Goji2100/Spresense-LCD-Board/DOC/IMG_4674.jpeg

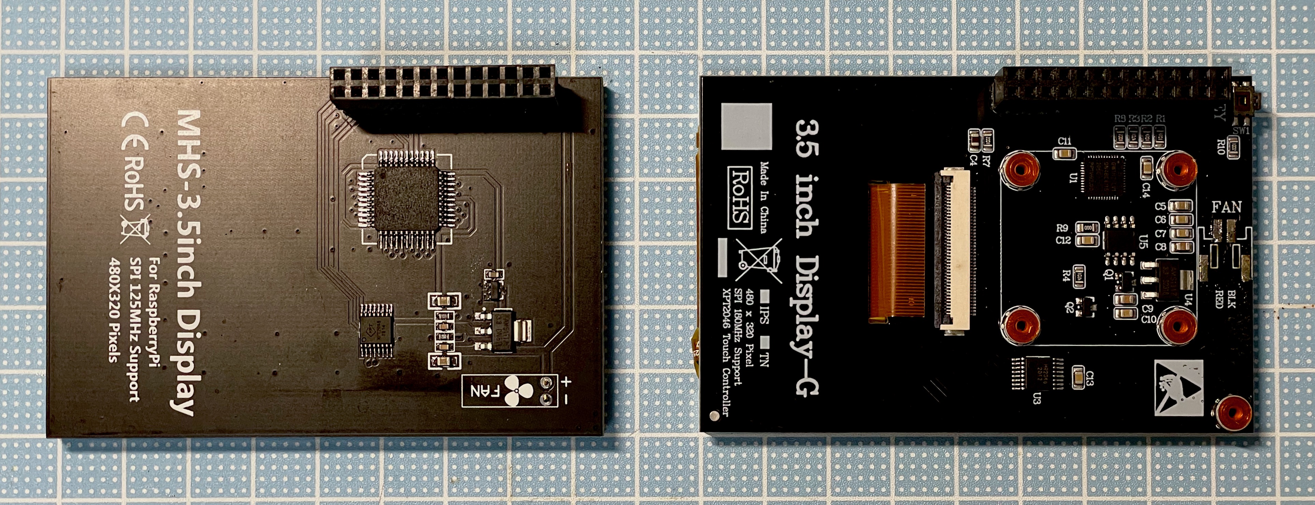
DOC/IMG_4674.jpeg
