Goji2100/Spresense-LCD-Board/DOC/IMG_4715.jpeg

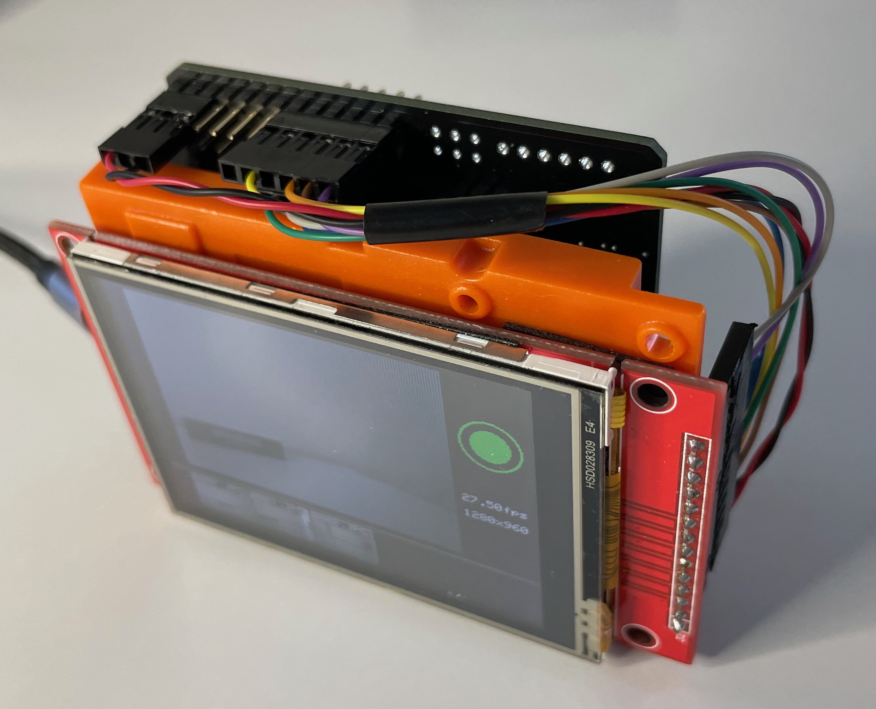
DOC/IMG_4715.jpeg
