Goji2100/Spresense-LCD-Board/DOC/IMG_4716.jpeg

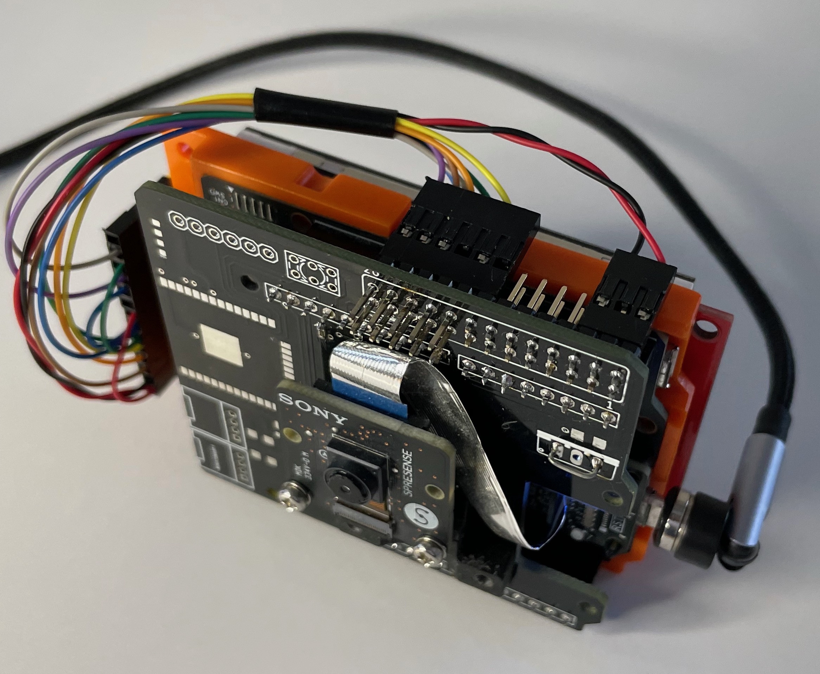
DOC/IMG_4716.jpeg
