Goji2100/Spresense-LCD-Board/DOC/IMG_4737.jpeg

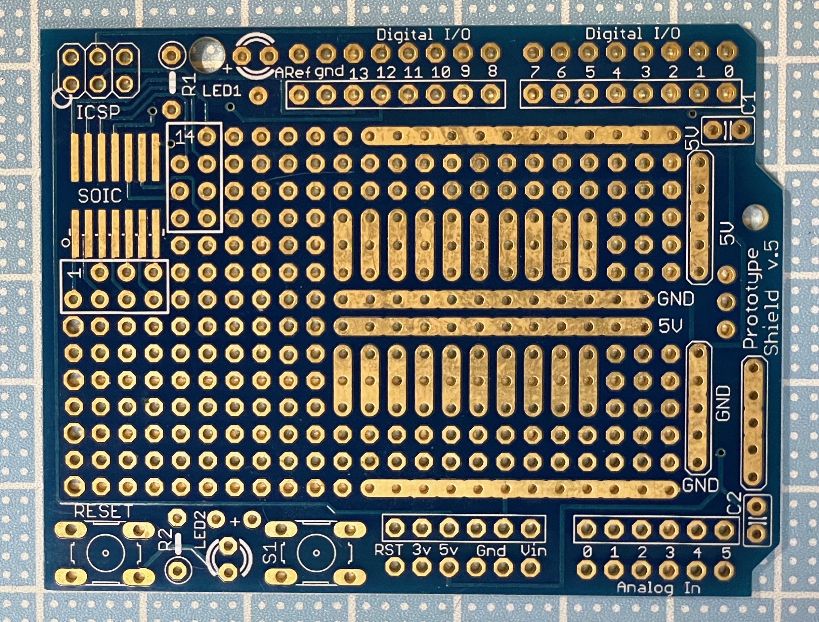
DOC/IMG_4737.jpeg
