Goji2100/Spresense-LCD-Board/DOC/IMG_4744.jpeg

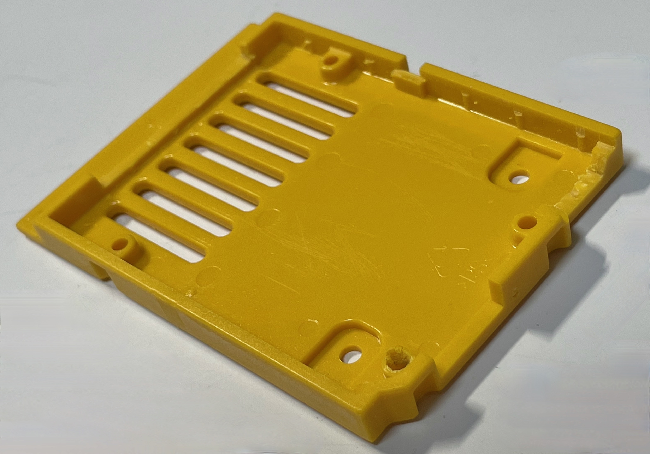
DOC/IMG_4744.jpeg
