Goji2100/Spresense-LCD-Board/camera_apitest/icon.h

const uint8_t ICON_heart[] = {
  0x00, 0x00, 0x00, 0x00, 0x00, // 1
  0x00, 0x00, 0x00, 0x00, 0x00, // 2
  0x00, 0x30, 0x00, 0xC0, 0x00, // 3
  0x00, 0x7C, 0x03, 0xF0, 0x00, // 4
  0x01, 0xFE, 0x07, 0xFC, 0x00, // 5
  0x03, 0xCF, 0x0F, 0x1E, 0x00, // 6
  0x07, 0x03, 0x9C, 0x07, 0x00, // 7
  0x0E, 0x01, 0xF8, 0x03, 0x80, // 8
  0x1C, 0x00, 0xF0, 0x01, 0x80, // 9
  0x18, 0x00, 0x60, 0x01, 0x80, //10
  0x18, 0x00, 0x00, 0x01, 0x80, //11
  0x18, 0x00, 0x00, 0x01, 0x80, //12
  0x18, 0x00, 0x00, 0x01, 0x80, //13
  0x18, 0x00, 0x00, 0x01, 0x80, //14
  0x1C, 0x00, 0x00, 0x03, 0x80, //15
  0x0C, 0x00, 0x00, 0x03, 0x00, //16
  0x0E, 0x00, 0x00, 0x07, 0x00, //17
  0x07, 0x00, 0x00, 0x0E, 0x00, //18
  0x03, 0x80, 0x00, 0x1C, 0x00, //19
  0x01, 0xC0, 0x00, 0x38, 0x00, //20
  0x00, 0xE0, 0x00, 0x70, 0x00, //21
  0x00, 0x70, 0x00, 0xE0, 0x00, //22
  0x00, 0x38, 0x01, 0xC0, 0x00, //23
  0x00, 0x1C, 0x03, 0x80, 0x00, //24
  0x00, 0x0E, 0x07, 0x00, 0x00, //25
  0x00, 0x07, 0x0E, 0x00, 0x00, //26
  0x00, 0x03, 0x9C, 0x00, 0x00, //27
  0x00, 0x01, 0xF8, 0x00, 0x00, //28
  0x00, 0x00, 0xF0, 0x00, 0x00, //29
  0x00, 0x00, 0x60, 0x00, 0x00, //30
  0x00, 0x00, 0x00, 0x00, 0x00, //31
  0x00, 0x00, 0x00, 0x00, 0x00  //32
};
